Toeffe3/IoT-Project/Device/src/ticks.h

/******************************************************************************/
/* Project:    Device                                                         */
/* File:       src/ticks.h                                                    */
/* Decription: Device tick header                                             */
/******************************************************************************/

#ifndef TICKS_H_
#define TICKS_H_

/***************************** Include files *******************************/
#include "header.h"

/*****************************    Defines    *******************************/

/*****************************   Variables   *******************************/
extern uint32_t ticks;

/*****************************   Functions   *******************************/
void ticks_init (void);

#endif /* TICKS_H_ */
